Muchajoe/The-AirFlow-Project/Hardware/PCB Front.png

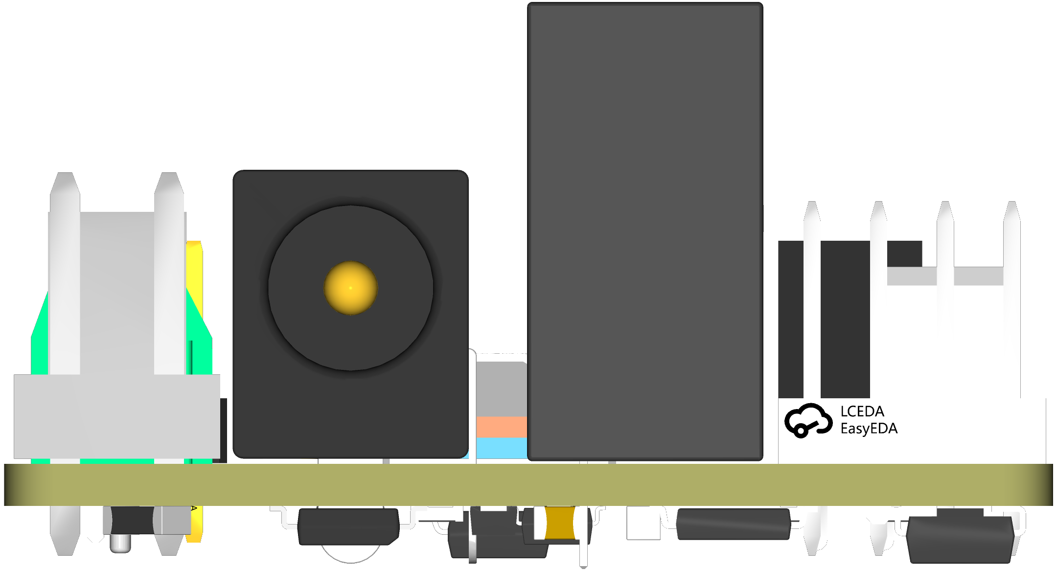
Hardware/PCB Front.png
