Muchajoe/The-AirFlow-Project/Hardware/PCB Side.png

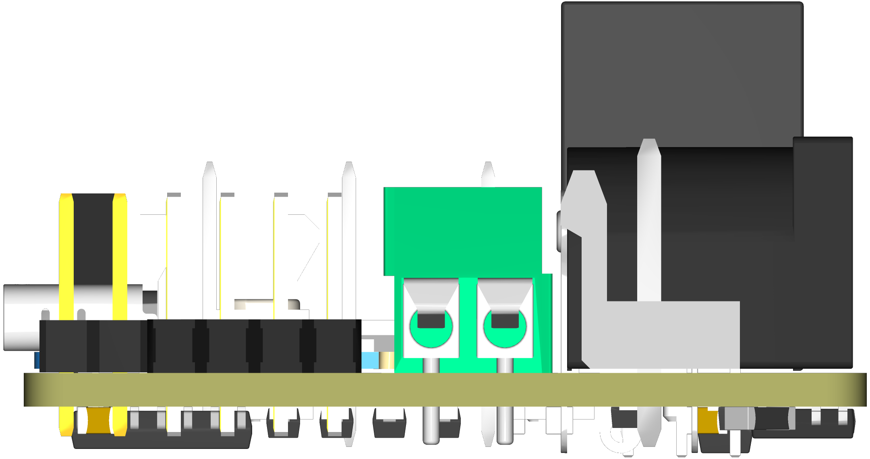
Hardware/PCB Side.png
