Muchajoe/The-AirFlow-Project/Hardware/PCB Top.png

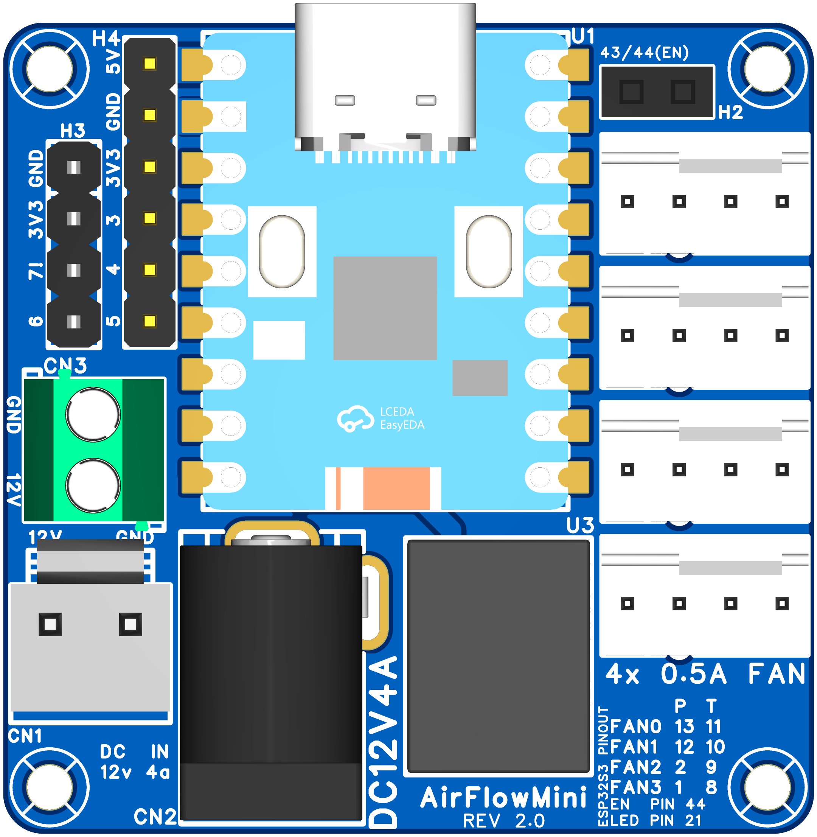
Hardware/PCB Top.png
