Muchajoe/The-AirFlow-Project/Images/PCB1.jpeg

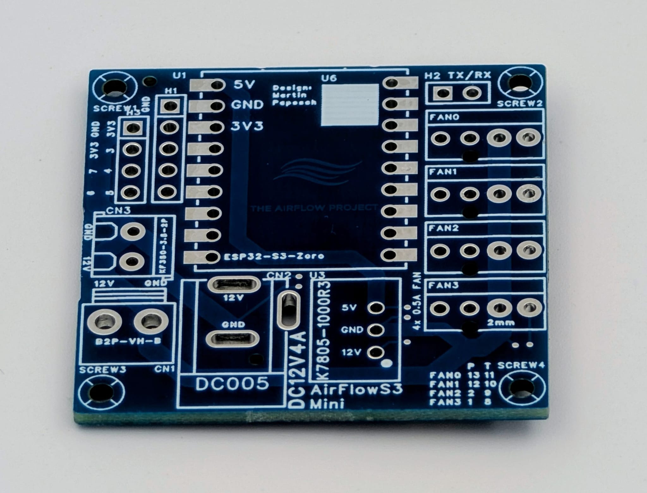
Images/PCB1.jpeg
