Muchajoe/The-AirFlow-Project/Images/PCB2.jpeg

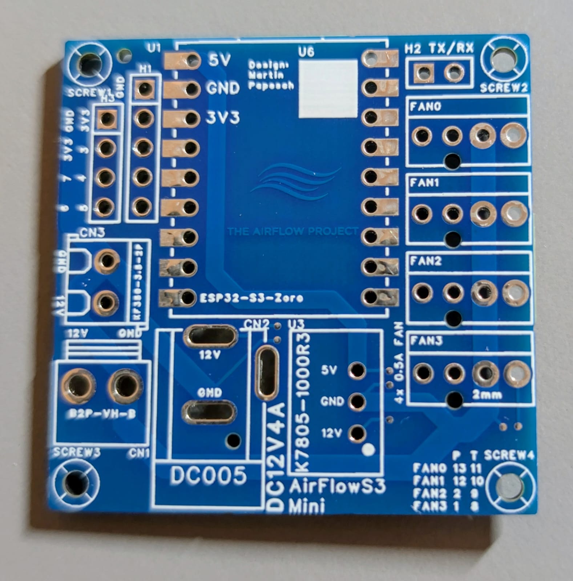
Images/PCB2.jpeg
