Muchajoe/The-AirFlow-Project/Images/PCB4.jpeg

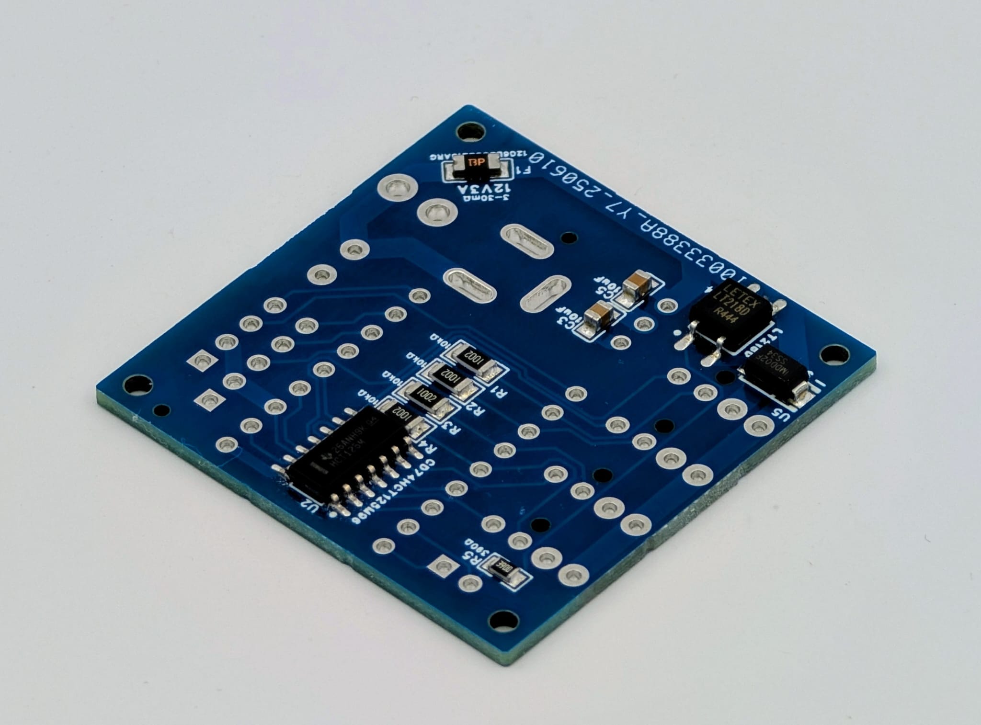
Images/PCB4.jpeg
