Muchajoe/The-AirFlow-Project/Images/PCB Rendering1.png

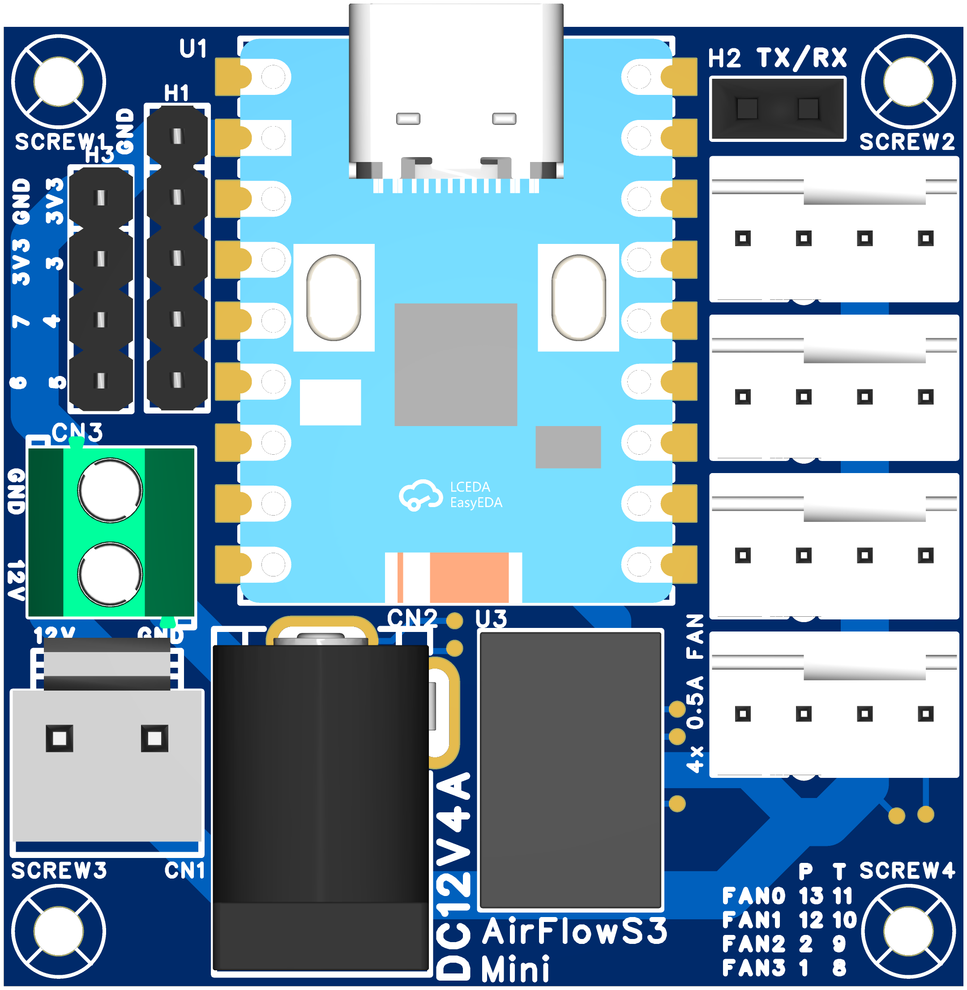
Images/PCB Rendering1.png
