Muchajoe/The-AirFlow-Project/Images/PCB Rendering2.png

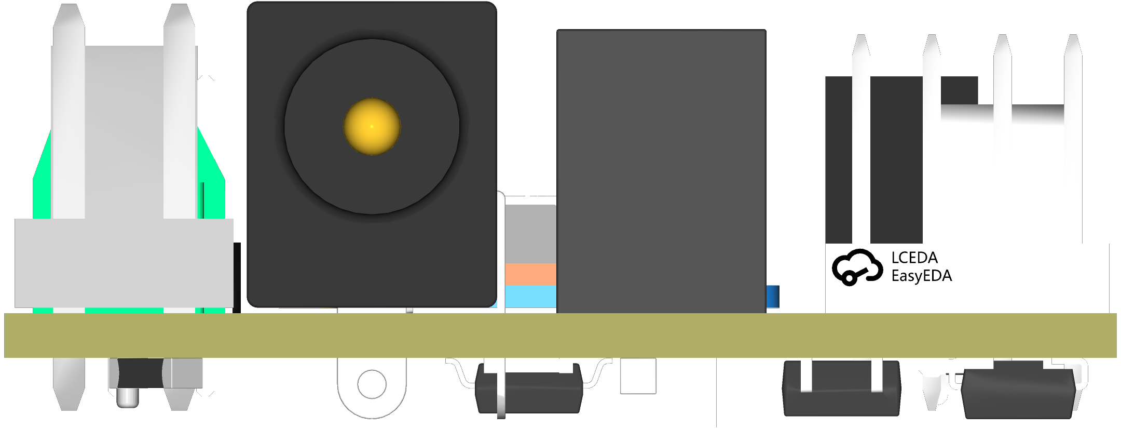
Images/PCB Rendering2.png
