Muchajoe/The-AirFlow-Project/Images/PCB Rendering3.png

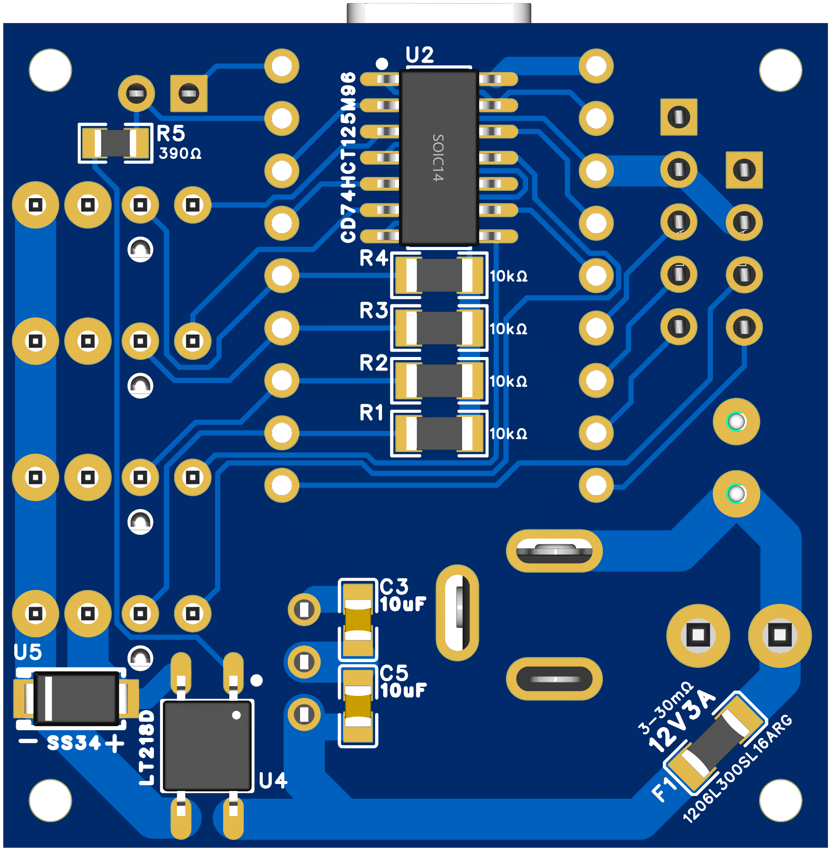
Images/PCB Rendering3.png
