Muchajoe/The-AirFlow-Project/Images/screen.png

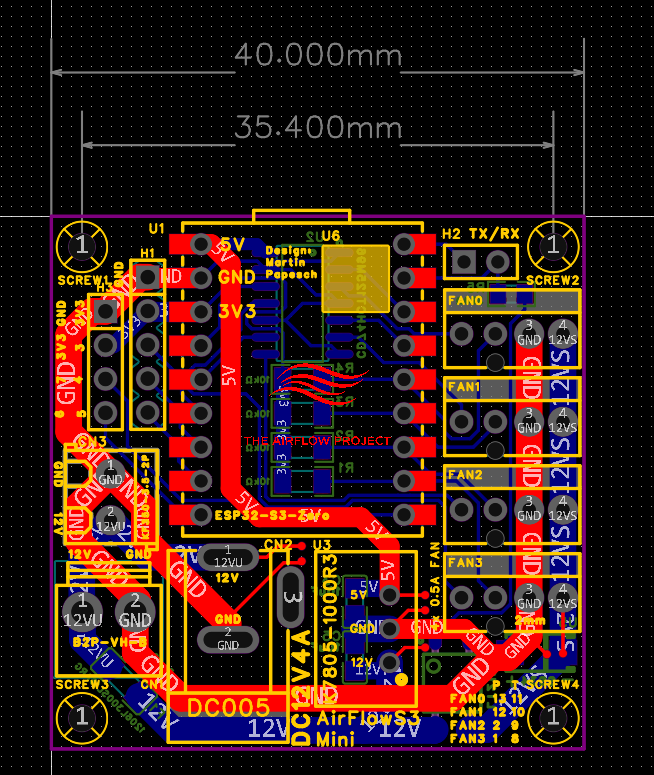
Images/screen.png
